joaoaluz/claude-mochi/firmware/claude_mochi/config.example.h

// Copie este arquivo para config.h e preencha com os seus dados.
// config.h está no .gitignore — a senha do Wi-Fi não vai para o repositório.
#pragma once

#define WIFI_SSID     "sua-rede-wifi"
#define WIFI_PASSWORD "sua-senha"

// Nome mDNS: o mochi responde em http://<MDNS_NAME>.local
#define MDNS_NAME     "mochi"
